Yusufss4/zone-based-indoor-positioning-and-hotdesk/Demo-Files/Assets/BordaAcademyTeam.png

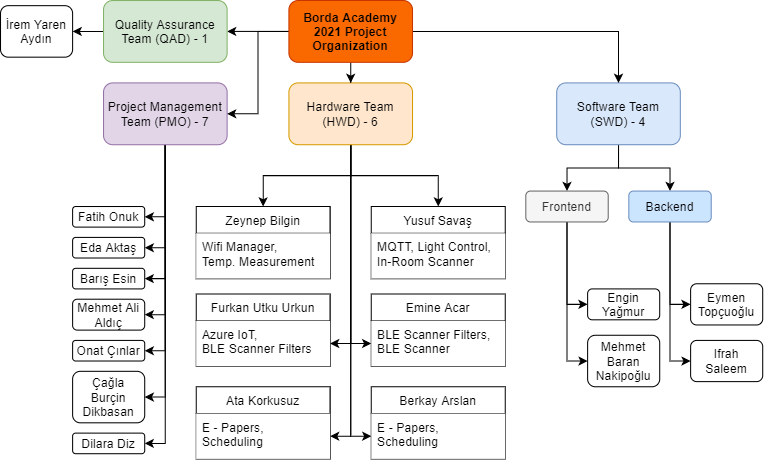
Demo-Files/Assets/BordaAcademyTeam.png
