Yusufss4/zone-based-indoor-positioning-and-hotdesk/DiagramFiles/ESP8266-WithLevelConverter_bb.png

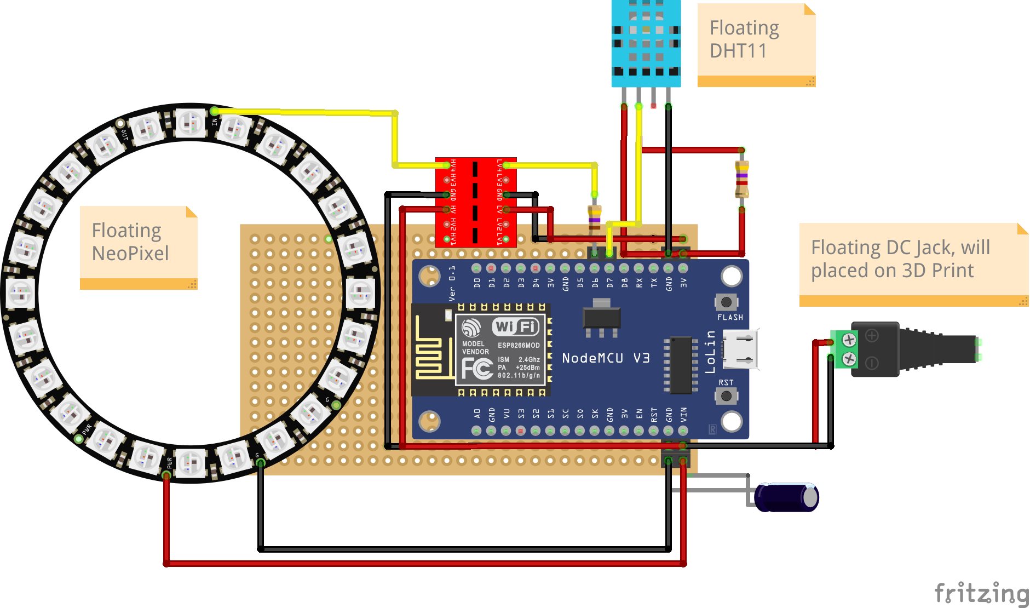
DiagramFiles/ESP8266-WithLevelConverter_bb.png
